chatelao/3dprinter_hacklab/18_32bit_main_board/Bigtreetech-SKR-V1-3-CPU-Upgrade-SKR.jpg

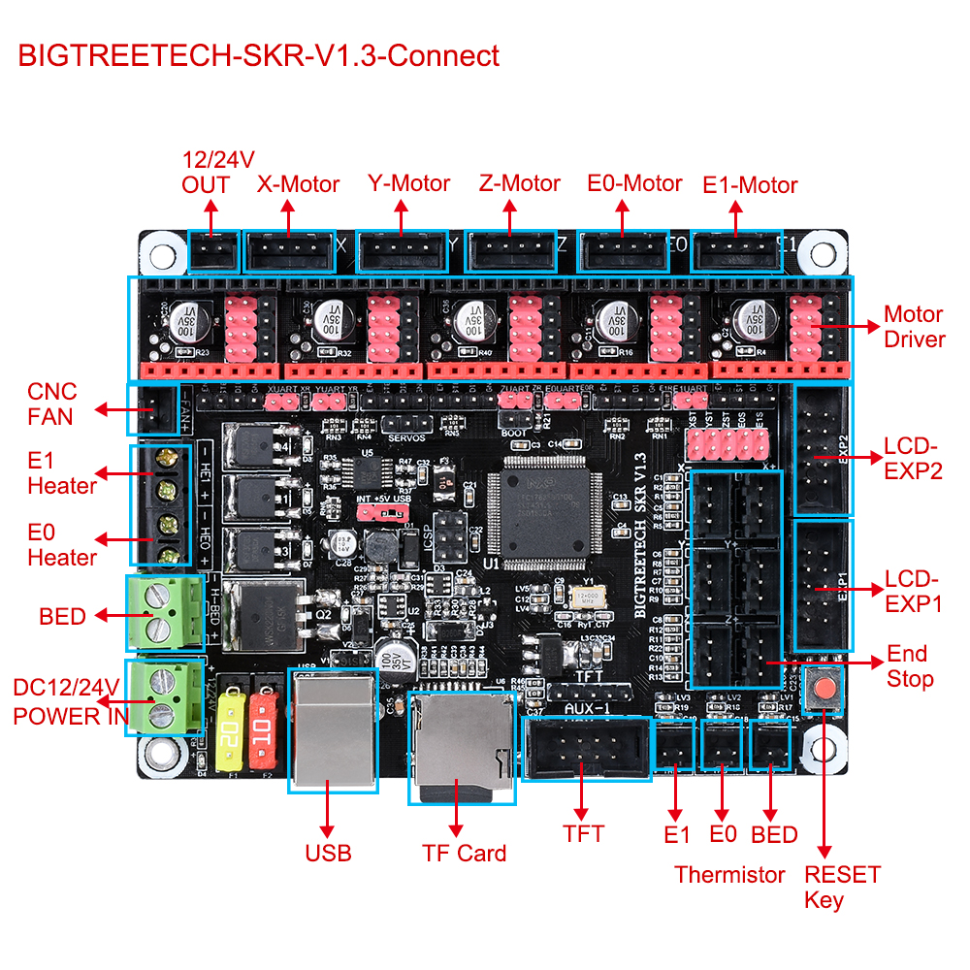
18_32bit_main_board/Bigtreetech-SKR-V1-3-CPU-Upgrade-SKR.jpg
