chatelao/3dprinter_hacklab/40_prusa_slicer/Sliced_Sample.PNG

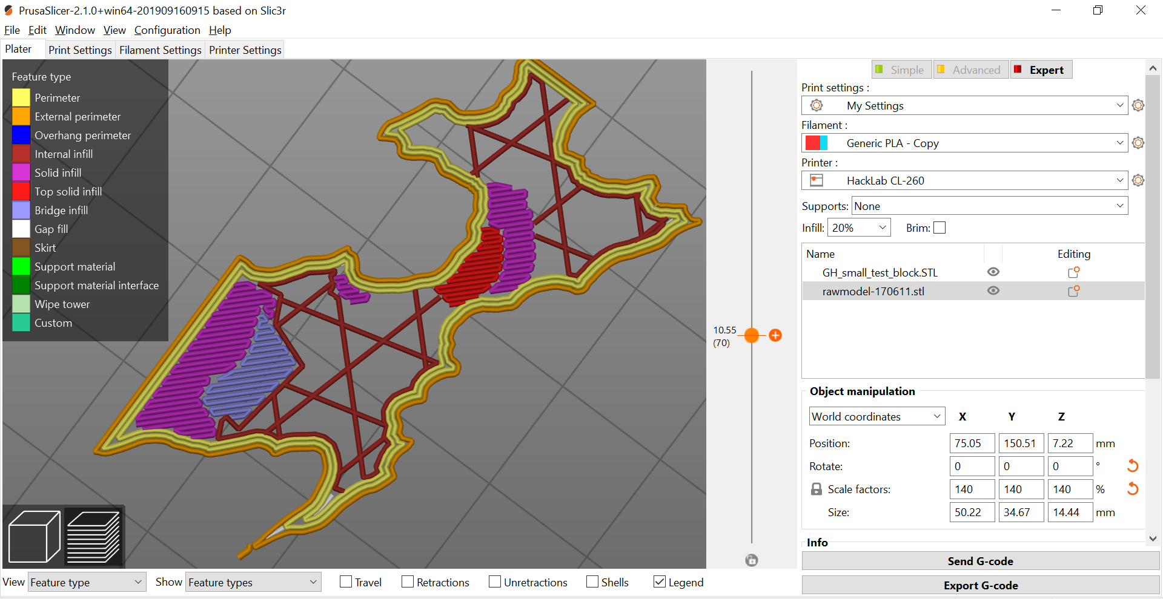
40_prusa_slicer/Sliced_Sample.PNG
