chatelao/3dprinter_hacklab/60_Pulley/Pulley_GT2_20Teeth_8MM.PNG

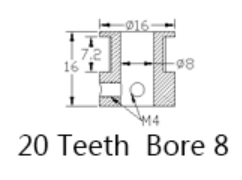
60_Pulley/Pulley_GT2_20Teeth_8MM.PNG
