chatelao/3dprinter_hacklab/35_calibration_block/GH_small_test_block.STL

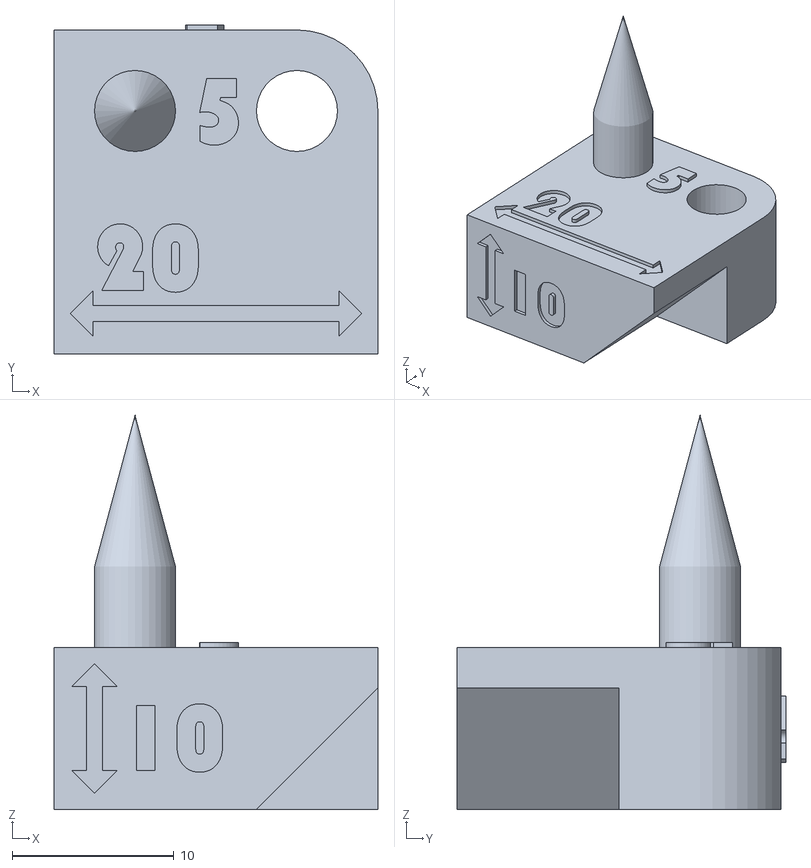
[picture p34: CAD file, 2019-12-25]
35_calibration_block/GH_small_test_block.STL
20.0 x 20.3 x 24.3
