chatelao/3dprinter_hacklab/36_all_in_one_test_big/AIl_In_One_3D_printer_test_micro.3mf

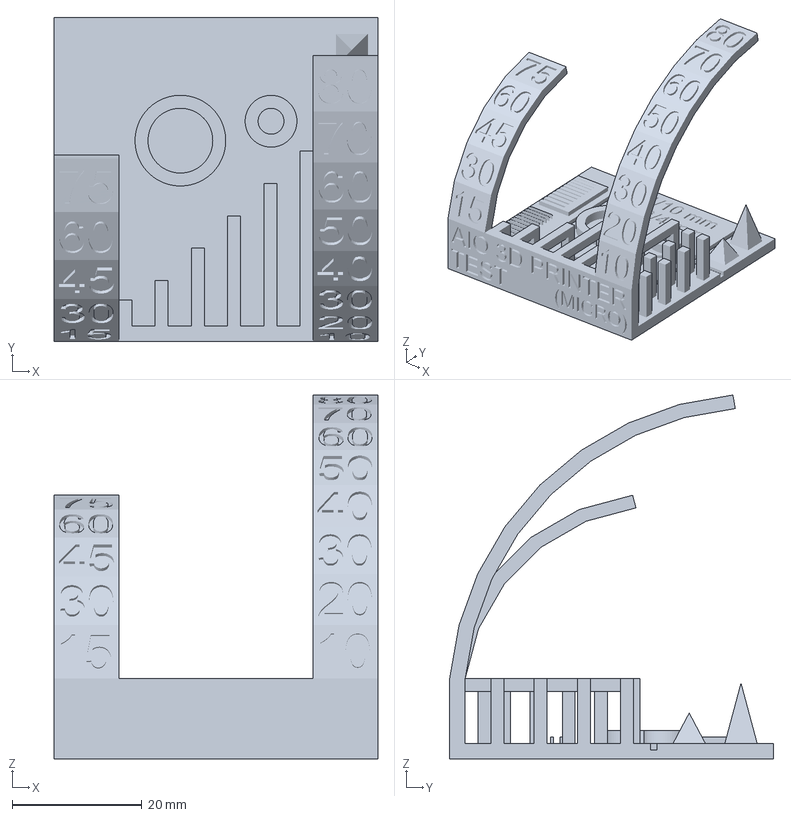
[picture p35: CAD file, 2020-01-13]
36_all_in_one_test_big/AIl_In_One_3D_printer_test_micro.3mf
50.0 x 50.0 x 56.2 mm
