chatelao/3dprinter_hacklab/00_printer_parts/Y_axle_seat_B.STL

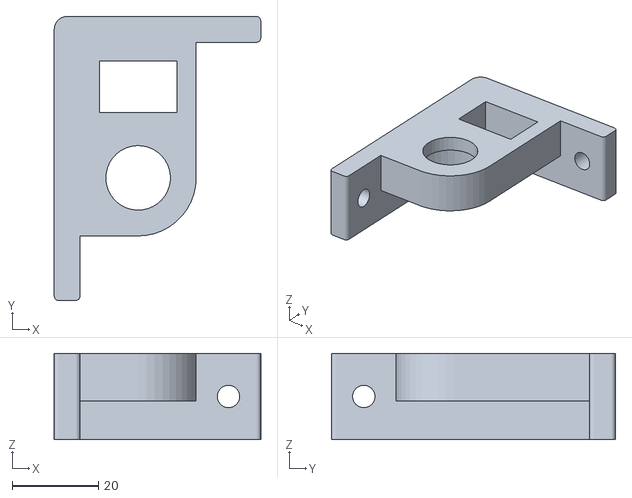
[picture p36: CAD file, 2019-12-09]
00_printer_parts/Y_axle_seat_B.STL
48.0 x 66.0 x 20.0
