chatelao/3dprinter_hacklab/01_xy_belt_holder/clamp.stl

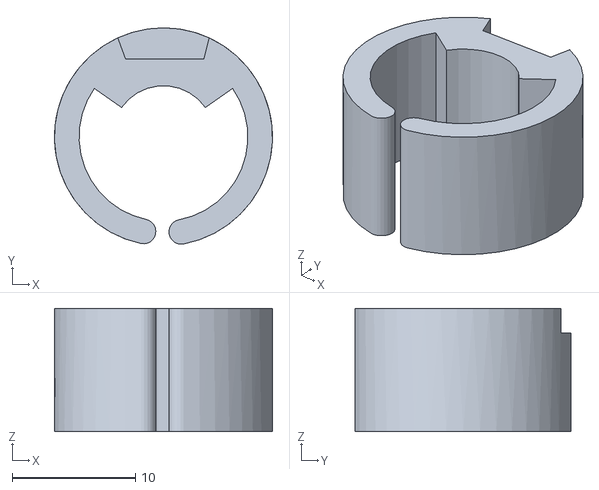
[picture p37: CAD file, 2019-12-06]
01_xy_belt_holder/clamp.stl
17.7 x 17.6 x 10.0
