chatelao/3dprinter_hacklab/03_z_axis_sensor_print/endstop_head.stl

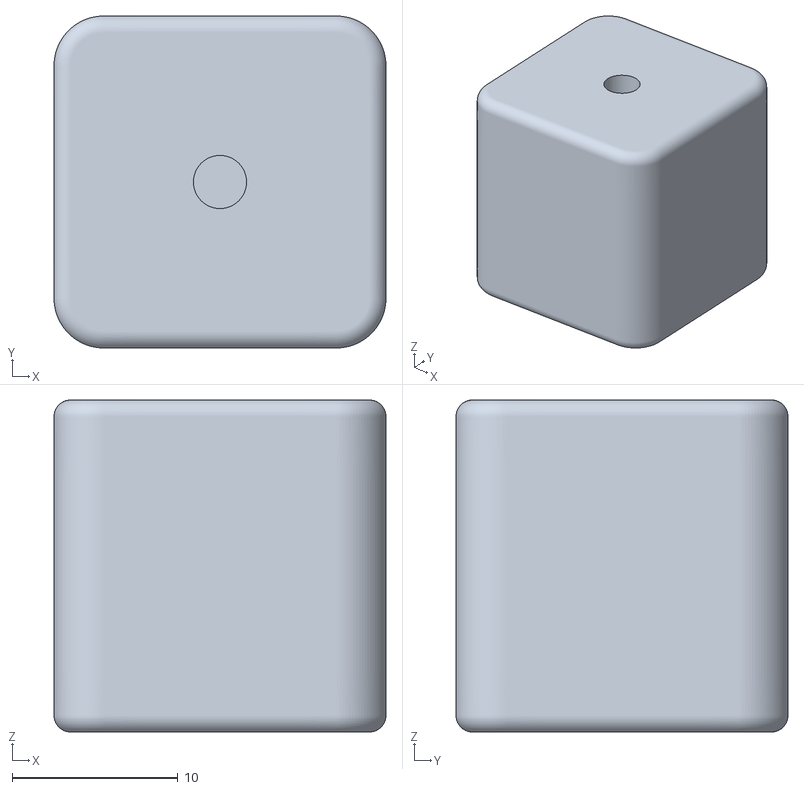
[picture p38: CAD file, 2019-12-04]
03_z_axis_sensor_print/endstop_head.stl
20.0 x 20.0 x 20.0
