chatelao/3dprinter_hacklab/06_fan_upgrade/fan-duct_vent_tgt_v4b.3mf

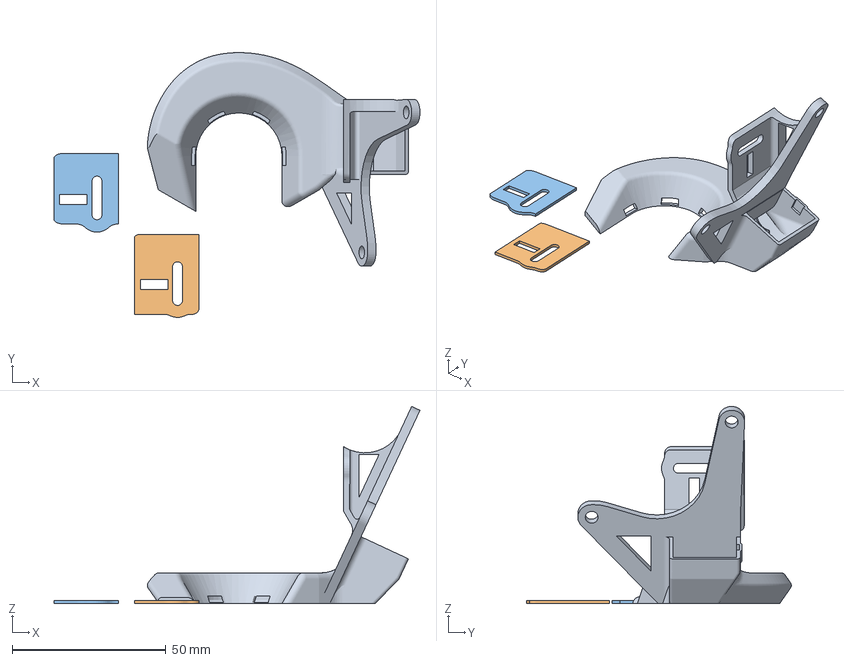
[picture p39: CAD file, 2019-12-28]
06_fan_upgrade/fan-duct_vent_tgt_v4b.3mf
119.0 x 86.1 x 64.1 mm
fan-duct_vent_tgt_v4b.STL
wedge_v4b.STL
wedge_v5b.STL
