chatelao/3dprinter_hacklab/08_belt_tensioner/belt_tie.stl

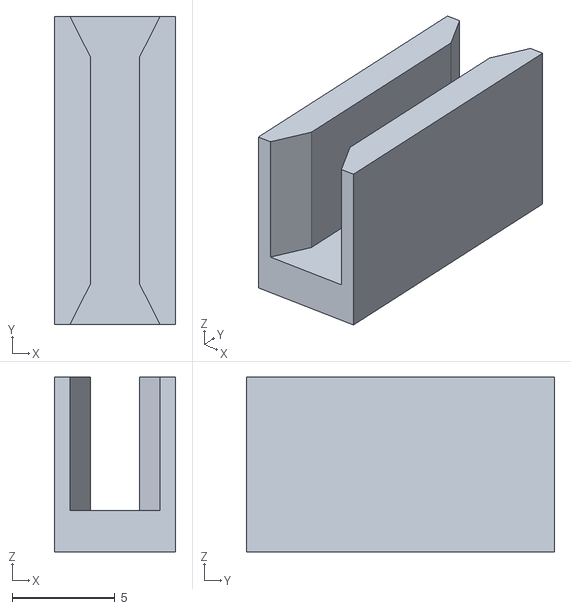
[picture p40: CAD file, 2020-01-17]
08_belt_tensioner/belt_tie.stl
5.90 x 15.0 x 8.50
