chatelao/3dprinter_hacklab/15_lcd_12864/Display_Support_Frame.stl

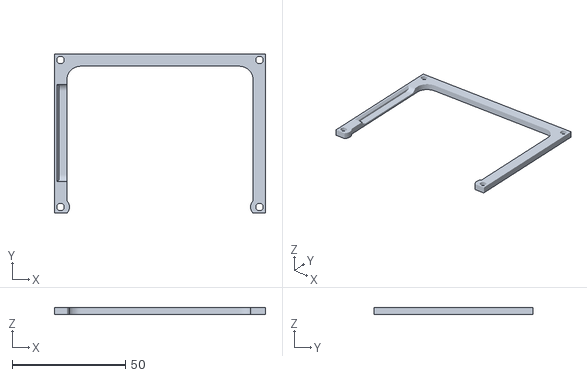
[picture p41: CAD file, 2019-12-06]
15_lcd_12864/Display_Support_Frame.stl
93.3 x 70.5 x 3.10
