chatelao/3dprinter_hacklab/20_filament_cleaner/Filament-Filter_L.3mf

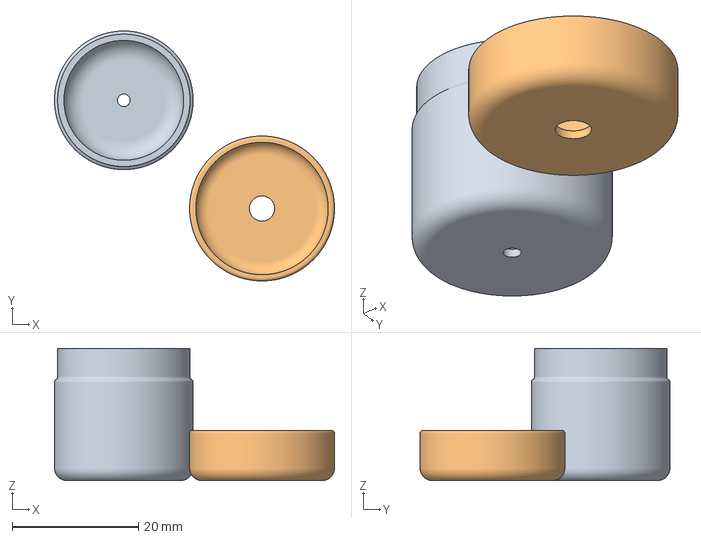
[picture p42: CAD file, 2019-12-25]
20_filament_cleaner/Filament-Filter_L.3mf
44.4 x 39.7 x 21.0 mm
Filament-Filter_L-A_v2.stl
Filament-Filter_L-B_v1.stl
