chatelao/3dprinter_hacklab/30_calibration_patterns/testbedcir2.stl

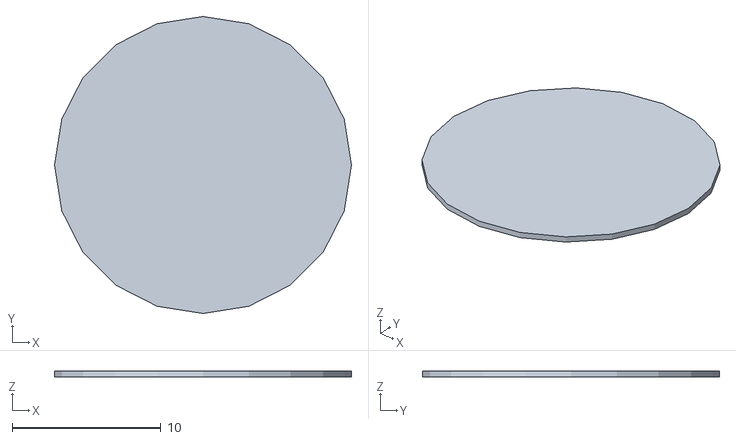
[picture p43: CAD file, 2020-01-16]
30_calibration_patterns/testbedcir2.stl
20.0 x 20.0 x 0.4
