chatelao/3dprinter_hacklab/00_printer_parts/UPS.STL

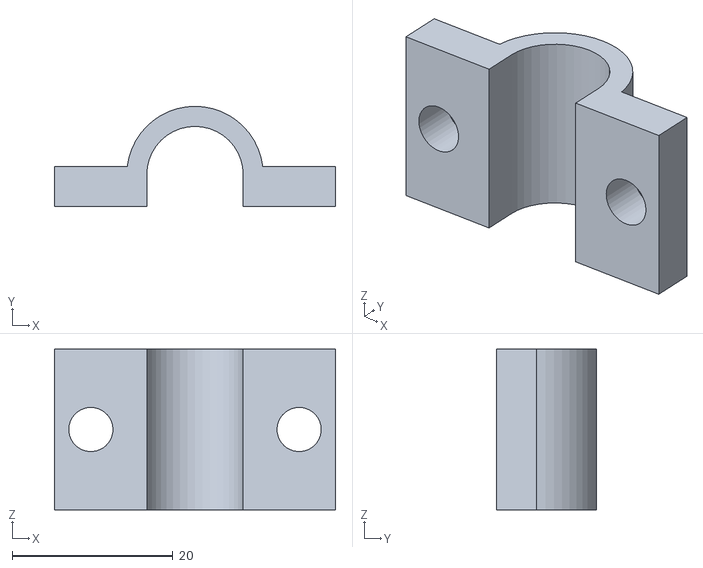
[picture p44: CAD file, 2019-12-09]
00_printer_parts/UPS.STL
35.0 x 12.5 x 20.0
