chatelao/3dprinter_hacklab/01_xy_belt_holder/Filler.stl

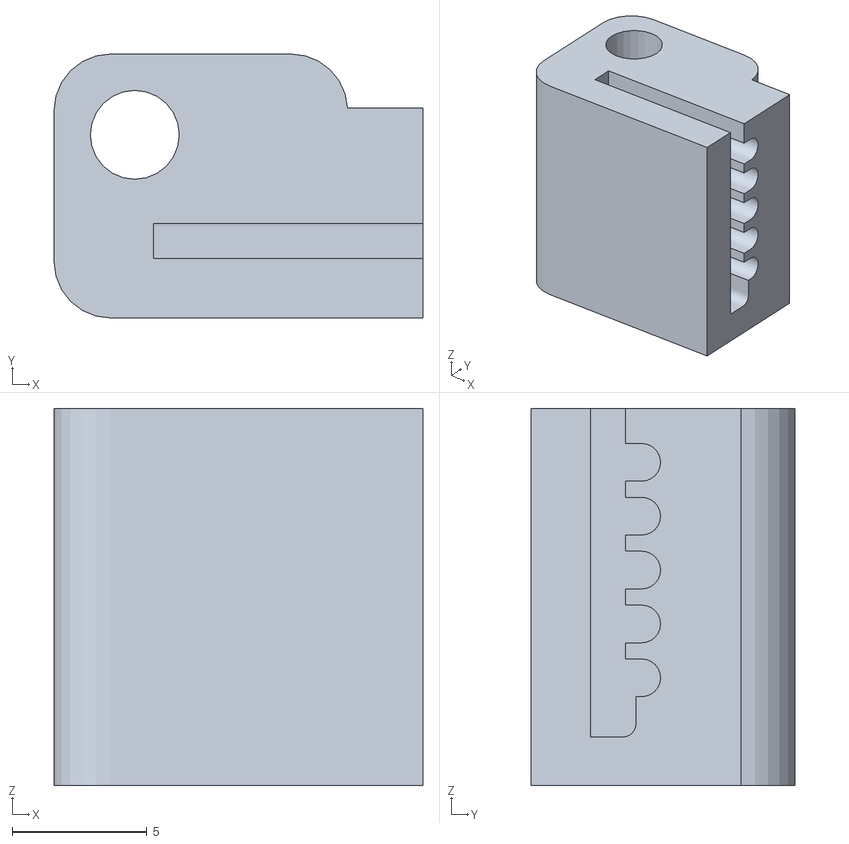
[picture p45: CAD file, 2019-12-06]
01_xy_belt_holder/Filler.stl
13.7 x 9.80 x 14.0
