chatelao/3dprinter_hacklab/06_fan_upgrade/wedge_v5b.STL

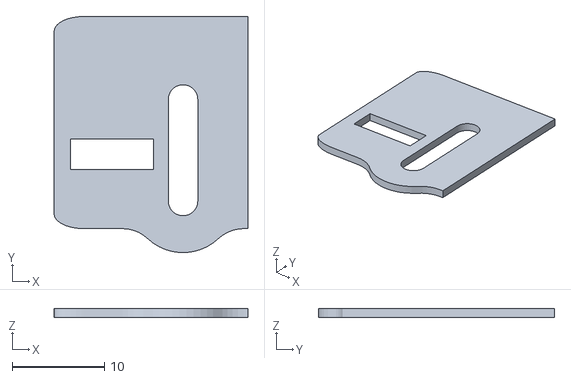
[picture p46: CAD file, 2019-12-28]
06_fan_upgrade/wedge_v5b.STL
21.0 x 25.6 x 1.00
