chatelao/3dprinter_hacklab/08_belt_tensioner/tensioner_small_part.stl

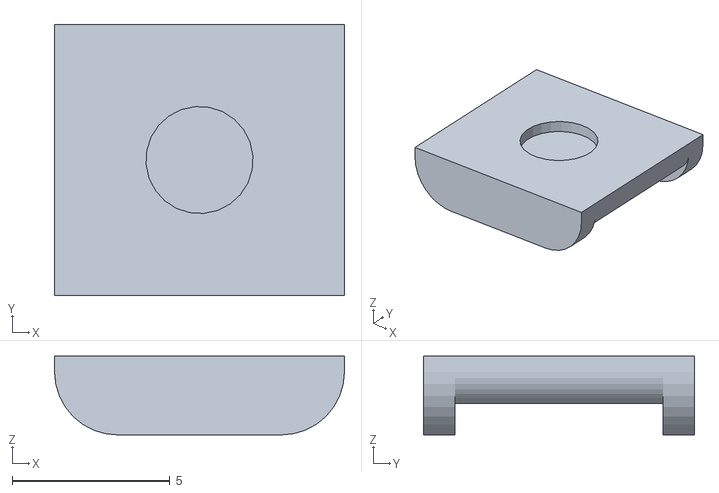
[picture p47: CAD file, 2020-01-17]
08_belt_tensioner/tensioner_small_part.stl
9.20 x 8.60 x 2.50
