chatelao/3dprinter_hacklab/09_filament_runout_sensor/filamentSensor.3mf

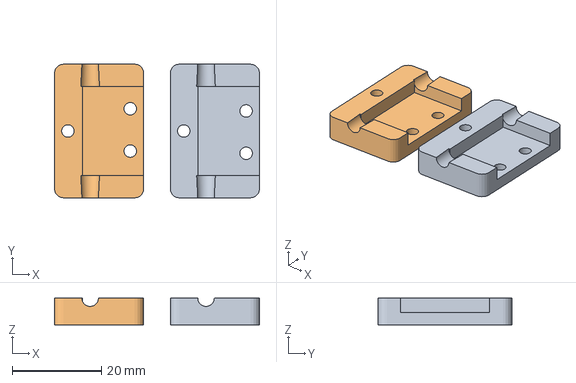
[picture p48: CAD file, 2020-01-17]
09_filament_runout_sensor/filamentSensor.3mf
46.0 x 30.0 x 6.00 mm
filamentSensorBottom175mm.stl
filamentSensorTop175mm.stl
