chatelao/3dprinter_hacklab/15_lcd_12864/Top_Shell.stl

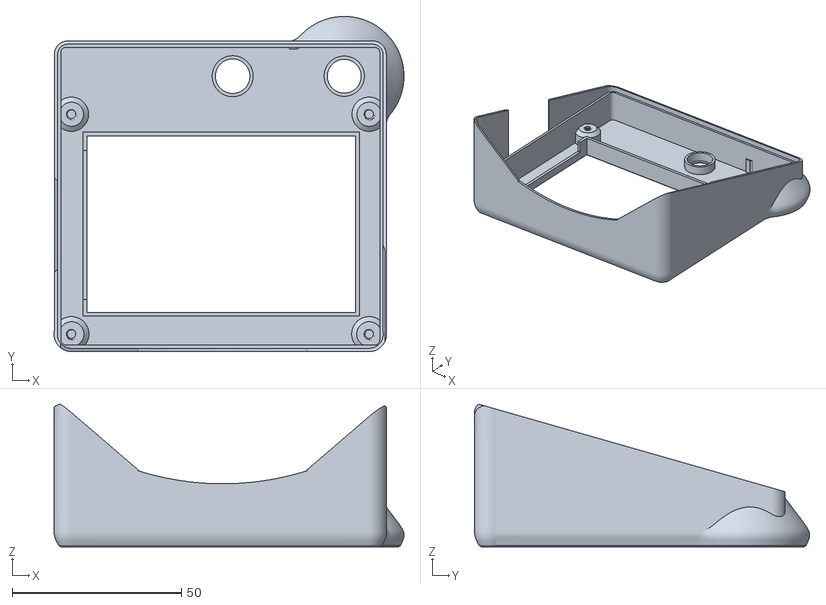
[picture p49: CAD file, 2019-12-06]
15_lcd_12864/Top_Shell.stl
103.5 x 99.1 x 42.2
