chatelao/3dprinter_hacklab/20_filament_cleaner/Filament-Filter_L-B_v1.3mf

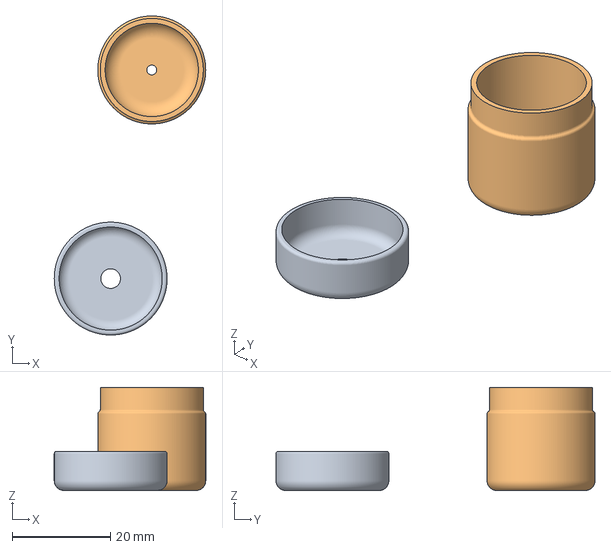
[picture p50: CAD file, 2019-12-25]
20_filament_cleaner/Filament-Filter_L-B_v1.3mf
30.9 x 65.0 x 21.0 mm
Filament-Filter_L-B_v1.stl
Filament-Filter_L-A_v2.stl
