chatelao/3dprinter_hacklab/30_calibration_patterns/testbedsq2.stl

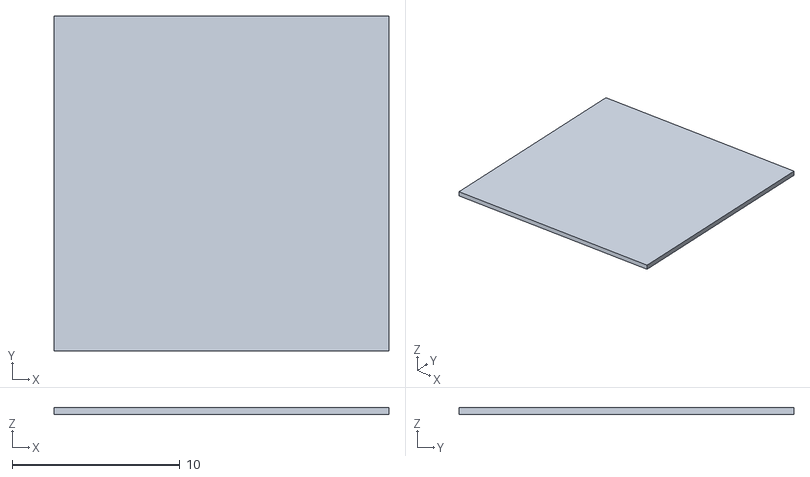
[picture p51: CAD file, 2020-01-16]
30_calibration_patterns/testbedsq2.stl
20.0 x 20.0 x 0.4
