chatelao/3dprinter_hacklab/00_printer_parts/Z_axle_seat.STL

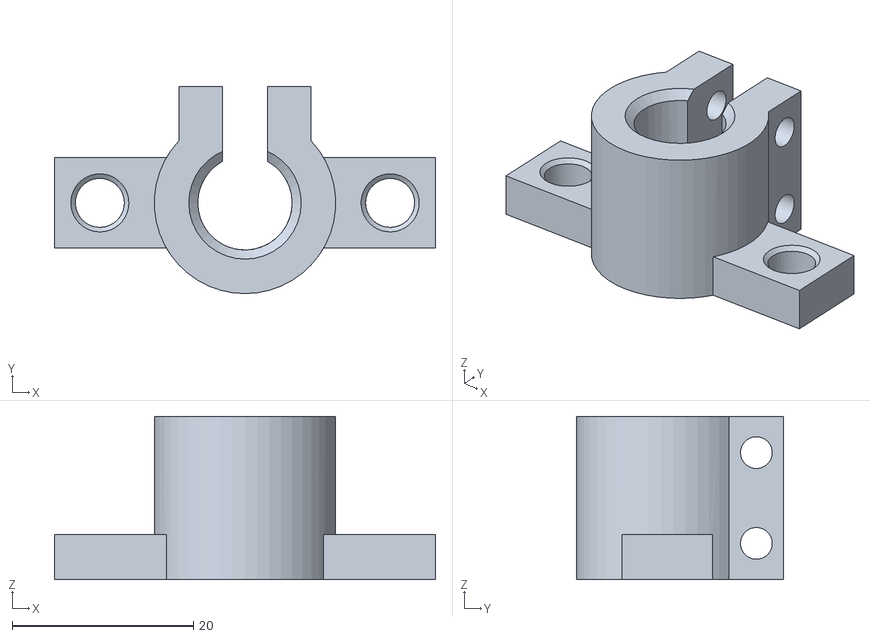
[picture p52: CAD file, 2019-12-09]
00_printer_parts/Z_axle_seat.STL
42.0 x 22.8 x 18.0
