chatelao/3dprinter_hacklab/08_belt_tensioner/tensioner_big_2.8mm.stl

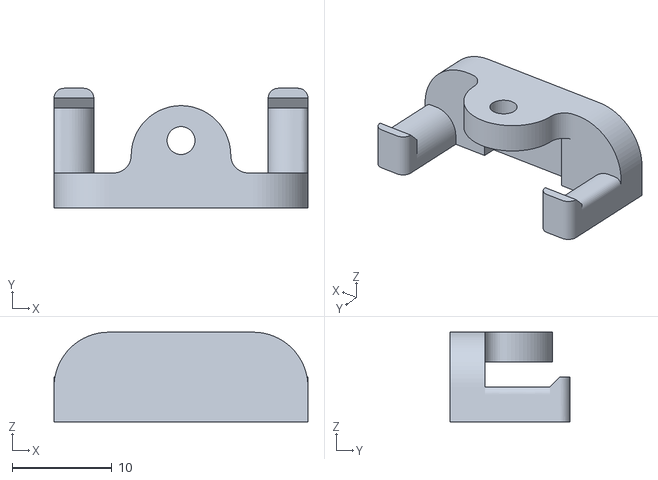
[picture p53: CAD file, 2020-01-17]
08_belt_tensioner/tensioner_big_2.8mm.stl
25.5 x 12.0 x 9.00
