chatelao/3dprinter_hacklab/15_lcd_12864/Rotary_Knob.stl

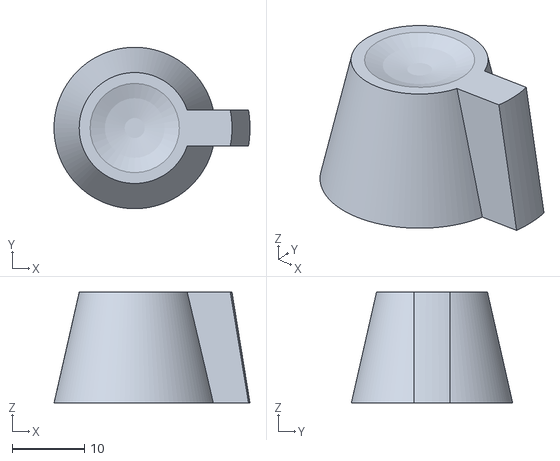
[picture p54: CAD file, 2019-12-06]
15_lcd_12864/Rotary_Knob.stl
27.2 x 22.4 x 15.4
