chatelao/3dprinter_hacklab/20_filament_cleaner/Filament-Filter_S-A_v2.stl

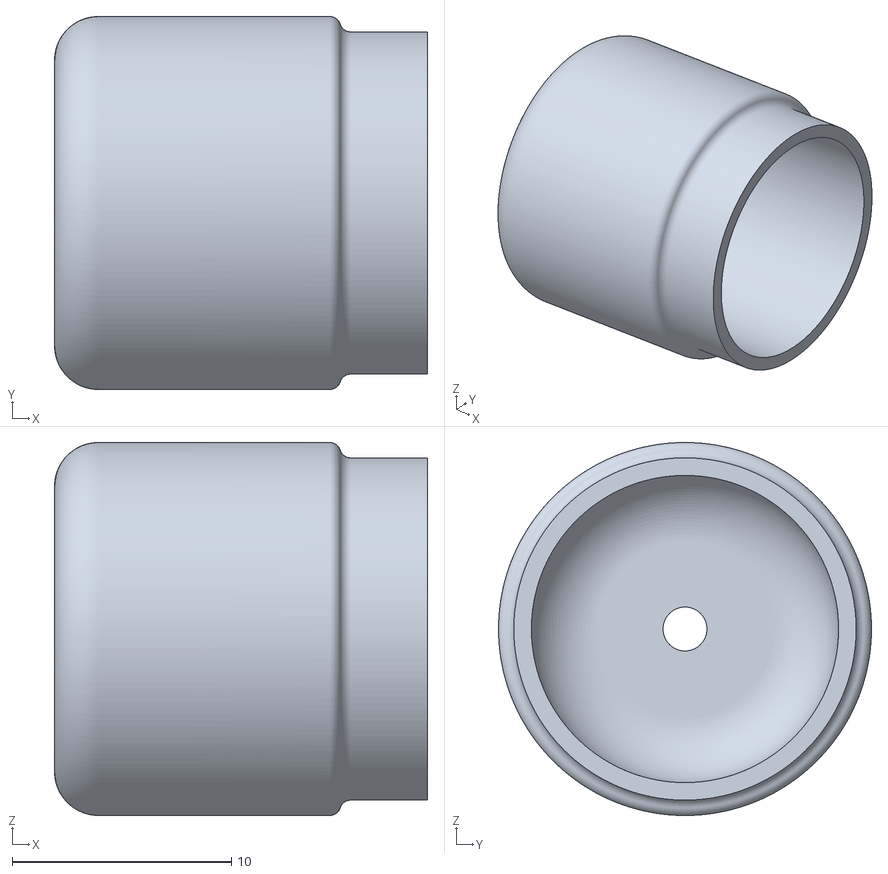
[picture p55: CAD file, 2019-12-05]
20_filament_cleaner/Filament-Filter_S-A_v2.stl
17.0 x 17.0 x 17.0
