chatelao/3dprinter_hacklab/30_calibration_patterns/testbedsq1.stl

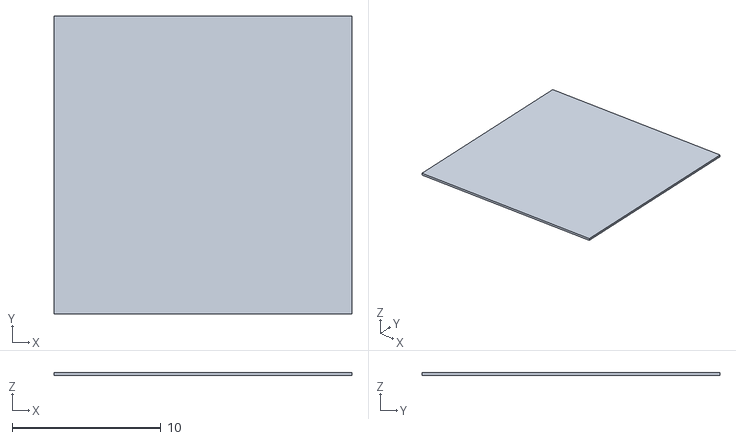
[picture p56: CAD file, 2020-01-16]
30_calibration_patterns/testbedsq1.stl
20.0 x 20.0 x 0.2
