chatelao/3dprinter_hacklab/08_belt_tensioner/tensioner_big_2.7mm_standard.3mf

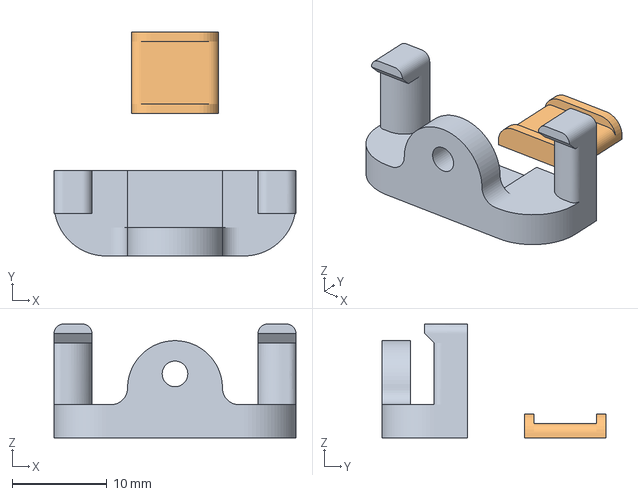
[picture p57: CAD file, 2020-01-17]
08_belt_tensioner/tensioner_big_2.7mm_standard.3mf
25.5 x 23.6 x 12.0 mm
tensioner_big_2.7mm_standard.stl
tensioner_small_part.stl
