chatelao/3dprinter_hacklab/15_lcd_12864/Bottom_Shell.stl

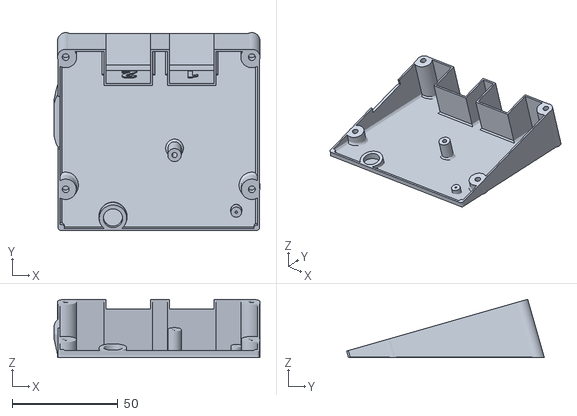
[picture p58: CAD file, 2019-12-06]
15_lcd_12864/Bottom_Shell.stl
97.4 x 93.5 x 27.6
