chatelao/3dprinter_hacklab/20_filament_cleaner/Filament-Filter_L-A_v2.stl

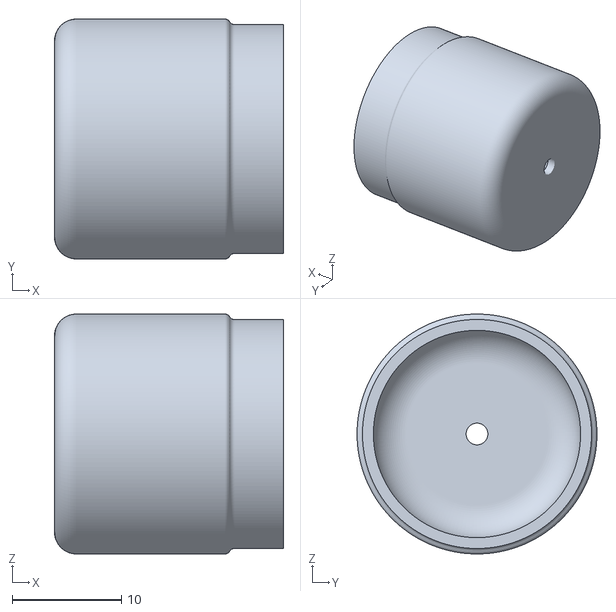
[picture p59: CAD file, 2019-12-05]
20_filament_cleaner/Filament-Filter_L-A_v2.stl
21.0 x 22.0 x 22.0
