chatelao/3dprinter_hacklab/30_calibration_patterns/30x30.stl

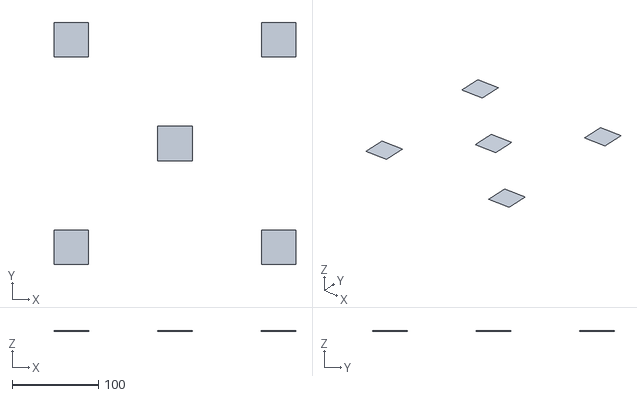
[picture p60: CAD file, 2019-12-04]
30_calibration_patterns/30x30.stl
280.0 x 280.0 x 0.2
