chatelao/3dprinter_hacklab/00_printer_parts/Mounting_plate.STL

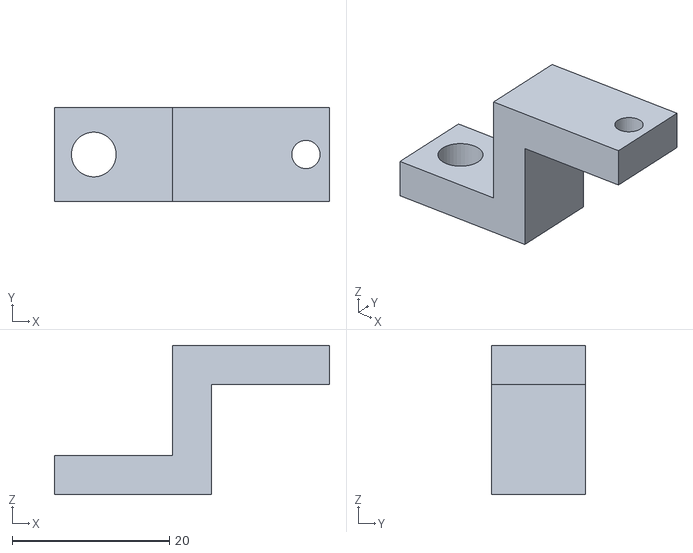
[picture p61: CAD file, 2019-12-09]
00_printer_parts/Mounting_plate.STL
35.0 x 12.0 x 19.0
