chatelao/3dprinter_hacklab/05_Upgrades_aller_Art/Riehmenspanner/_RiemenspannerReP.3mf

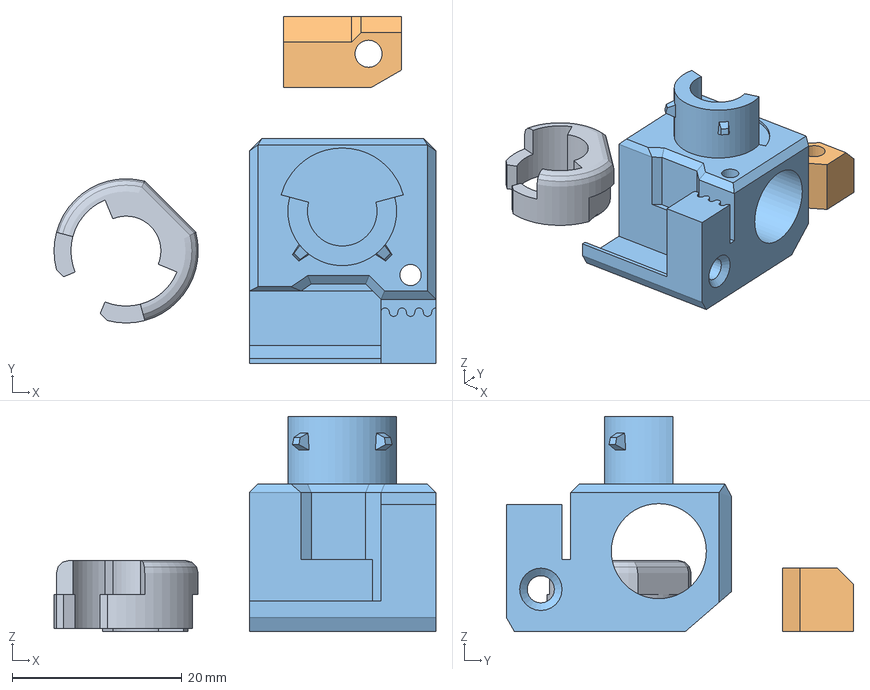
[picture p62: CAD file, 2020-01-17]
05_Upgrades_aller_Art/Riehmenspanner/_RiemenspannerReP.3mf
45.0 x 40.9 x 25.4 mm
180129_RiemenspannerP3.stl
180129_Riemenspanner-ReP2.stl
180129_Riemenspanner-ReP1.stl
