chatelao/3dprinter_hacklab/30_calibration_patterns/20x20.stl

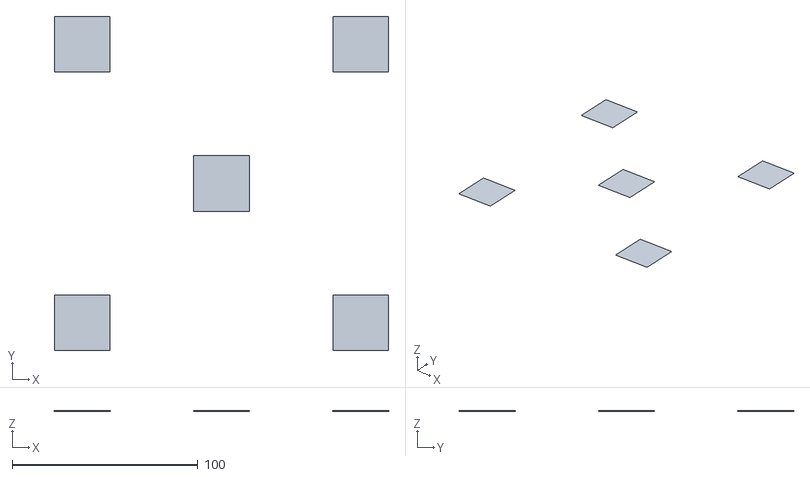
[picture p63: CAD file, 2019-12-04]
30_calibration_patterns/20x20.stl
180.0 x 180.0 x 0.2
