chatelao/3dprinter_hacklab/00_printer_parts/Blocks.STL

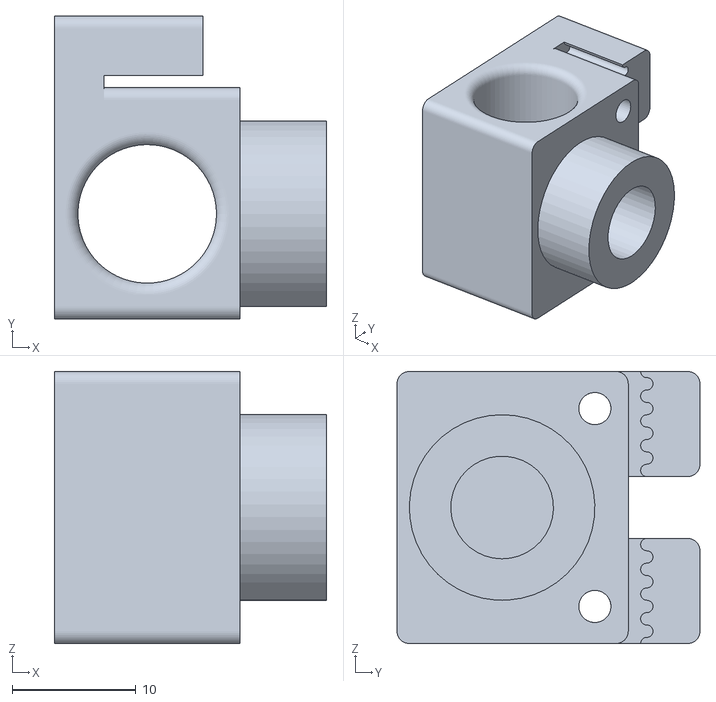
[picture p64: CAD file, 2019-12-09]
00_printer_parts/Blocks.STL
22.0 x 24.5 x 22.0
