chatelao/3dprinter_hacklab/00_printer_parts/End_stop.STL

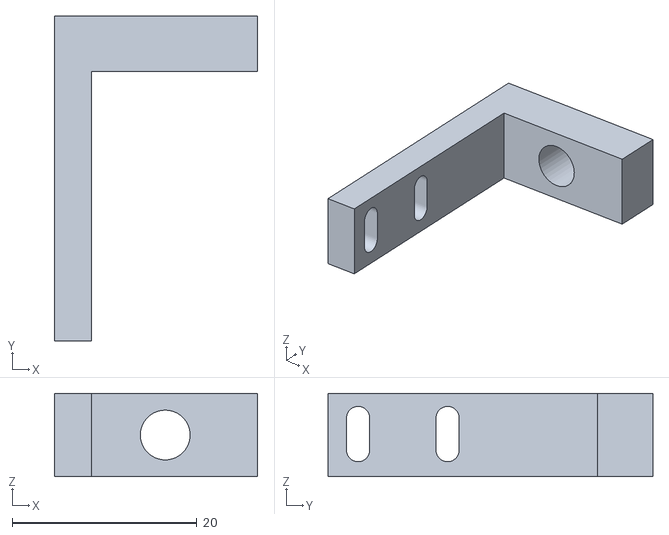
[picture p65: CAD file, 2019-12-09]
00_printer_parts/End_stop.STL
22.0 x 35.2 x 9.00
