chatelao/3dprinter_hacklab/00_printer_parts/Z_end_stop_B.STL

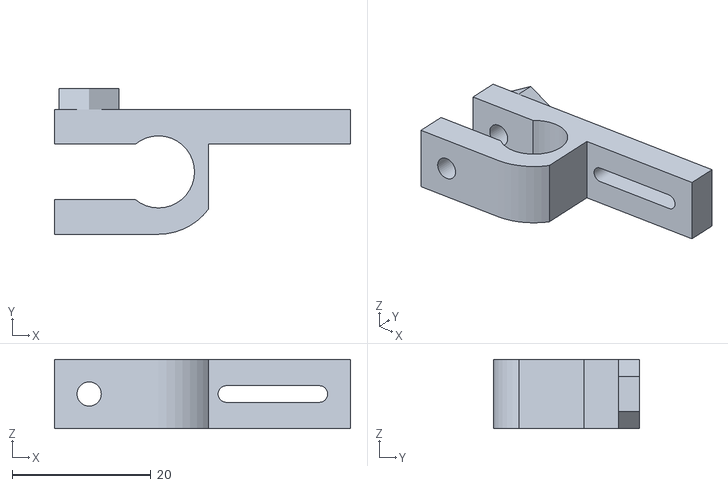
[picture p66: CAD file, 2019-12-09]
00_printer_parts/Z_end_stop_B.STL
42.7 x 21.0 x 10.0
