chatelao/3dprinter_hacklab/00_printer_parts/Axis_calibrator.STL

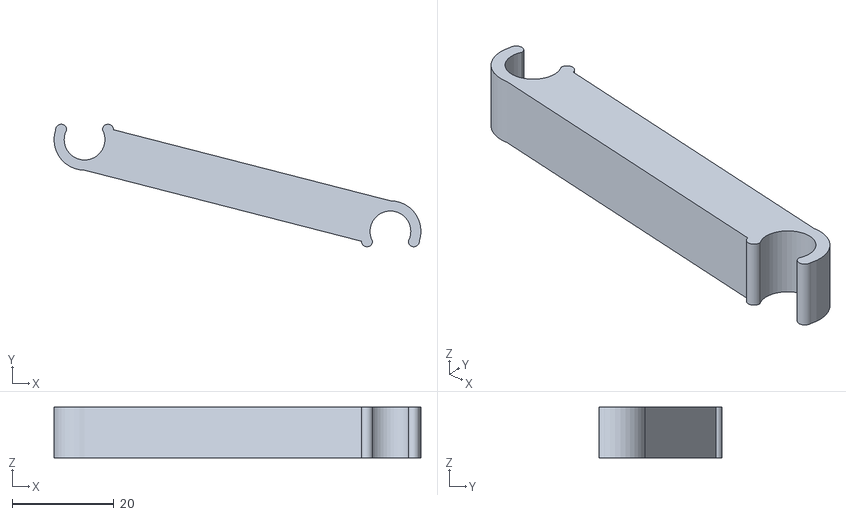
[picture p67: CAD file, 2019-12-09]
00_printer_parts/Axis_calibrator.STL
72.0 x 24.0 x 10.0
