chatelao/3dprinter_hacklab/00_printer_parts/X_axle_seat.STL

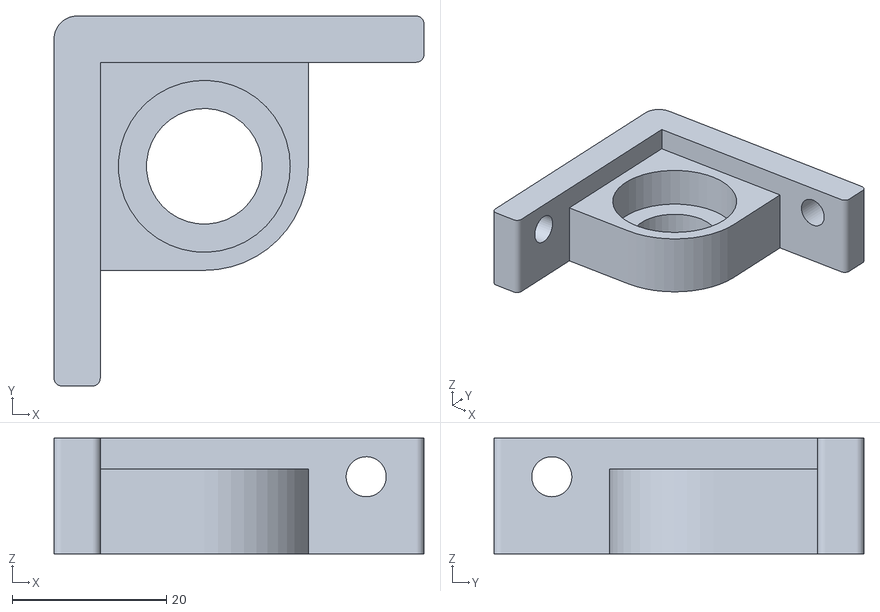
[picture p68: CAD file, 2019-12-09]
00_printer_parts/X_axle_seat.STL
48.0 x 48.0 x 15.0
