chatelao/3dprinter_hacklab/00_printer_parts/Carriage.STL

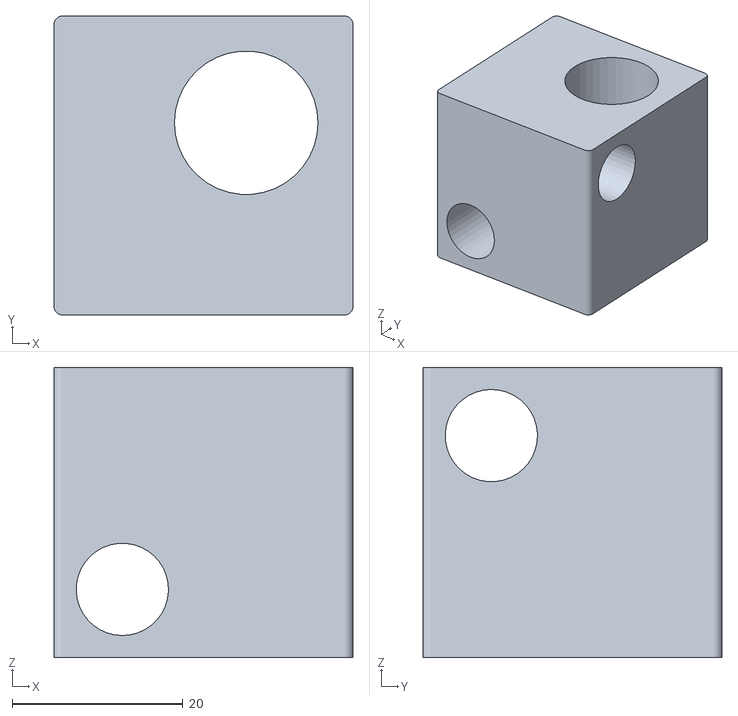
[picture p69: CAD file, 2019-12-09]
00_printer_parts/Carriage.STL
35.0 x 35.0 x 34.0
