chatelao/3dprinter_hacklab/00_printer_parts/3010_fan.STL

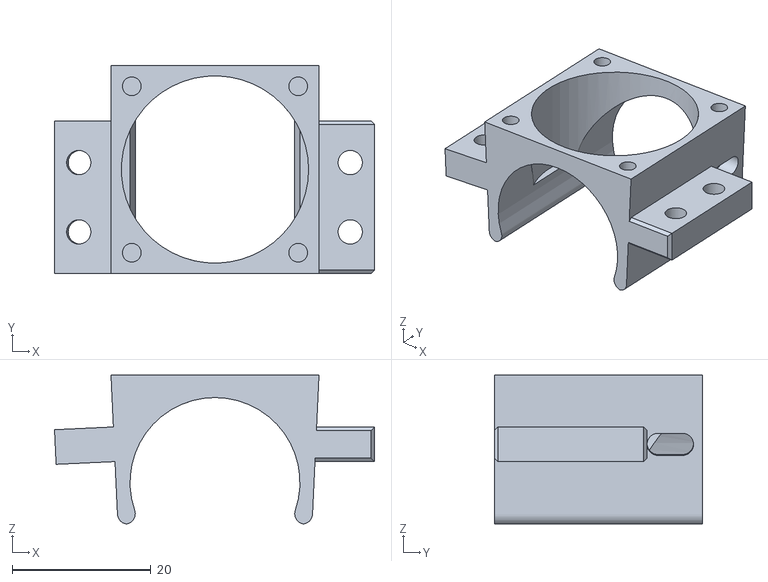
[picture p70: CAD file, 2019-12-09]
00_printer_parts/3010_fan.STL
46.1 x 30.0 x 21.5
