chatelao/3dprinter_hacklab/00_printer_parts/Z_end_stop_A.STL

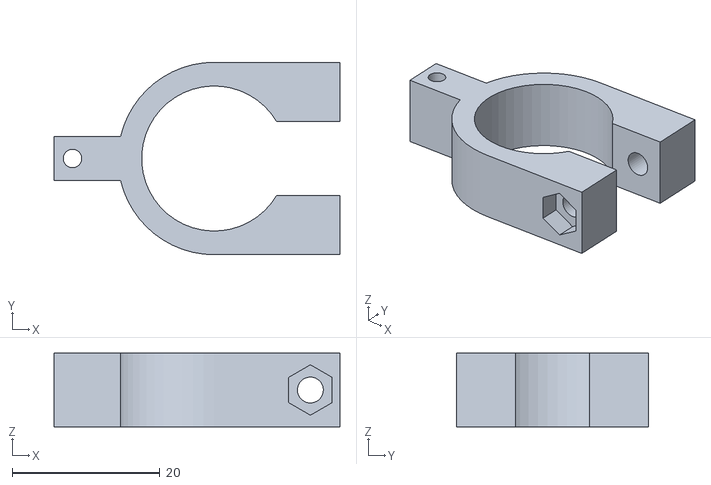
[picture p71: CAD file, 2019-12-09]
00_printer_parts/Z_end_stop_A.STL
38.6 x 26.0 x 10.0
