chatelao/3dprinter_hacklab/00_printer_parts/extruder_A.stl

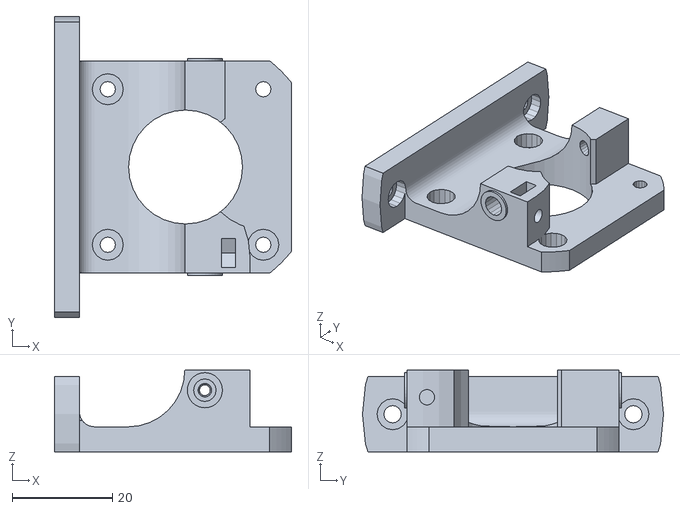
[picture p72: CAD file, 2019-12-06]
00_printer_parts/extruder_A.stl
47.3 x 60.0 x 16.3
