chatelao/3dprinter_hacklab/00_printer_parts/extruder_B.stl

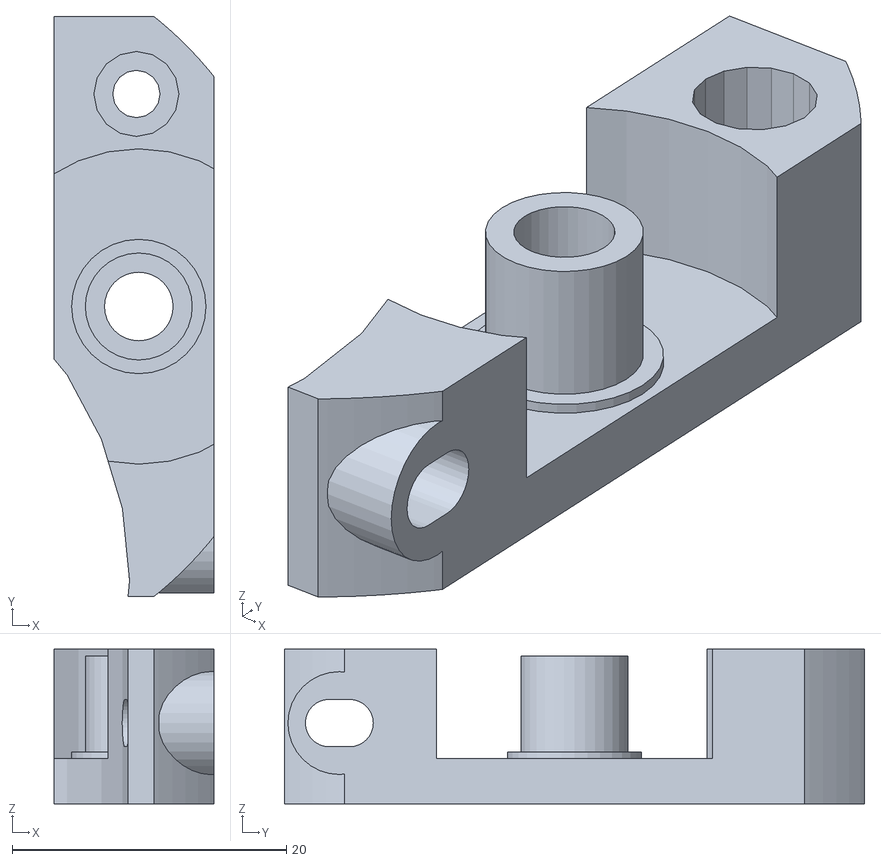
[picture p73: CAD file, 2019-12-06]
00_printer_parts/extruder_B.stl
11.6 x 42.3 x 11.3
